Bernardik226/espnokia-phone/docs/assets/dash-status.png

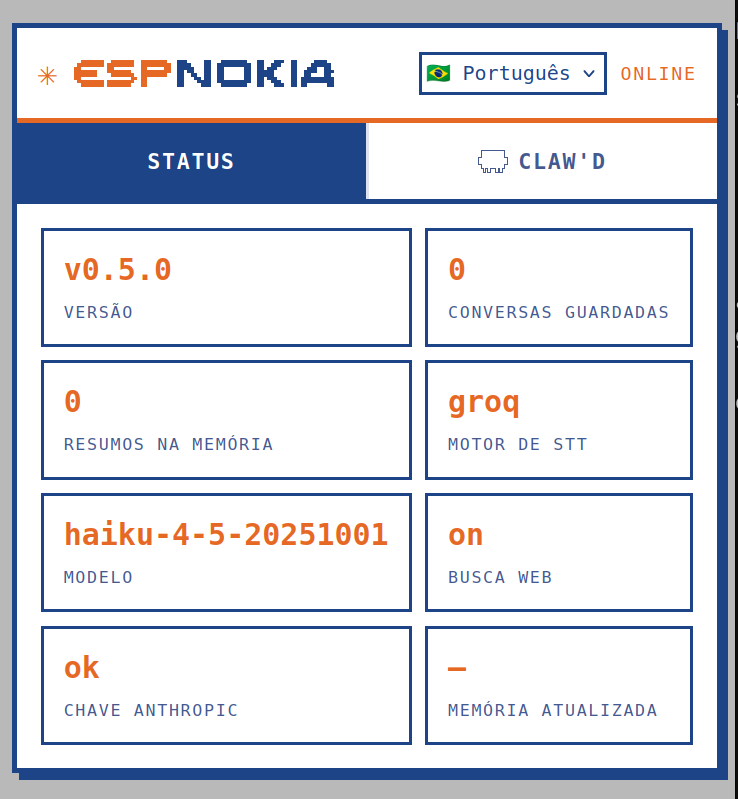
docs/assets/dash-status.png
