Bernardik226/espnokia-phone/docs/assets/photo-copa-menu.jpg

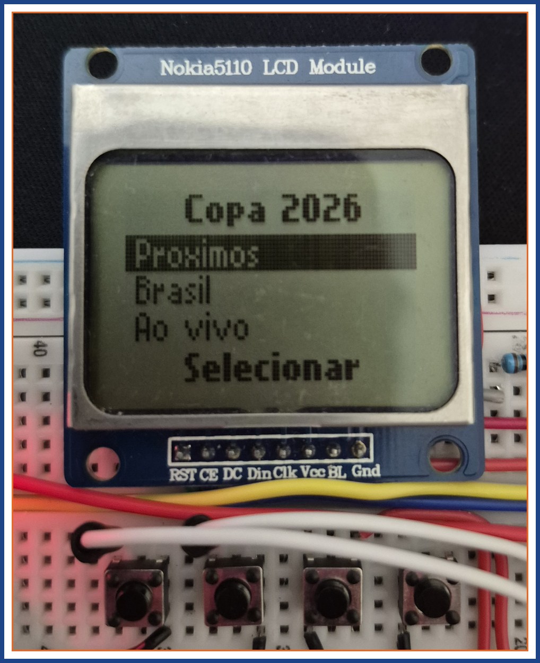
docs/assets/photo-copa-menu.jpg
