Bernardik226/espnokia-phone/docs/assets/photo-standby.jpg

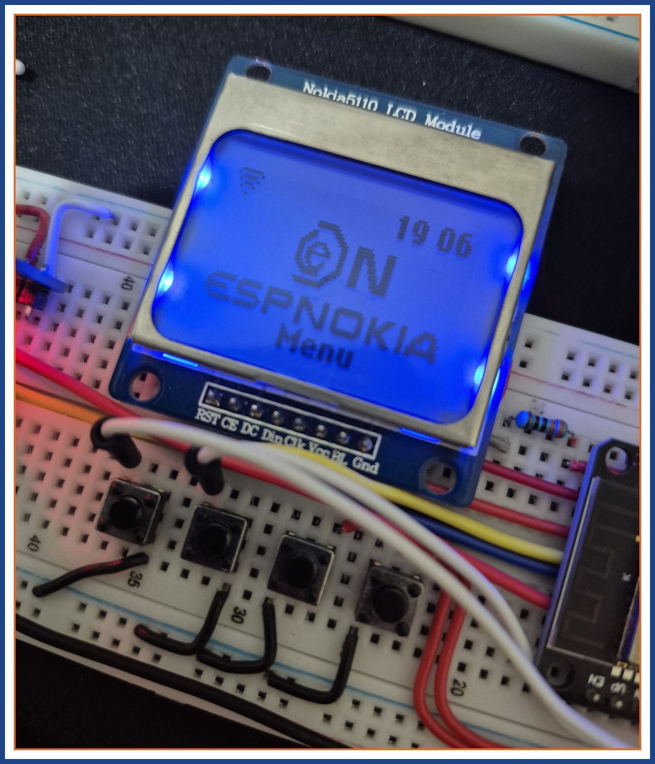
docs/assets/photo-standby.jpg
