Bernardik226/espnokia-phone/docs/assets/photos/clawd-listen.png

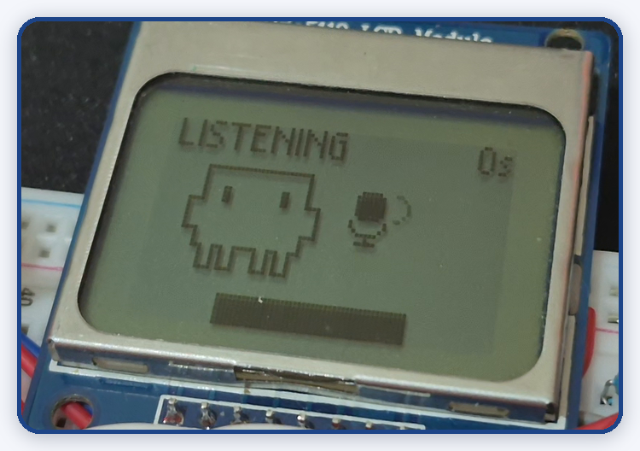
docs/assets/photos/clawd-listen.png
