Bernardik226/espnokia-phone/docs/assets/photos/clawd-reply.png

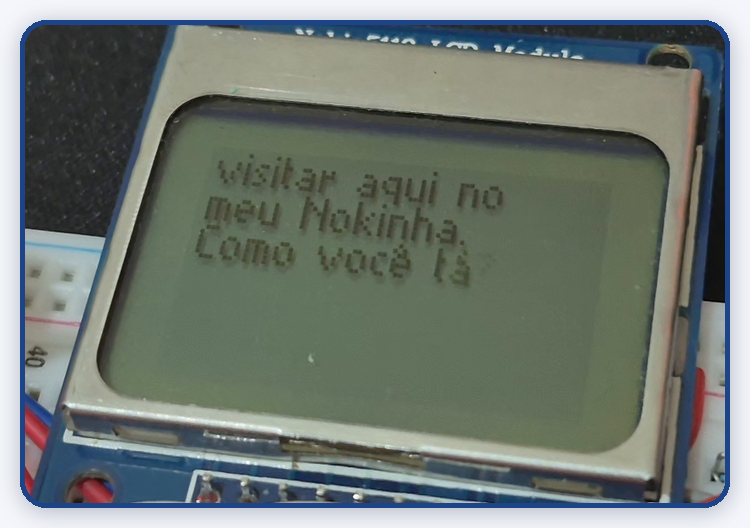
docs/assets/photos/clawd-reply.png
