Bernardik226/espnokia-phone/docs/assets/photos/clock.png

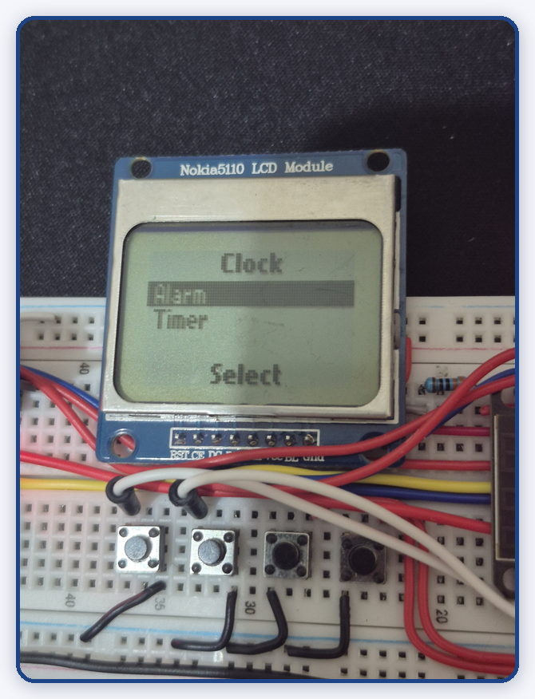
docs/assets/photos/clock.png
