Bernardik226/espnokia-phone/docs/assets/photos/connections.png

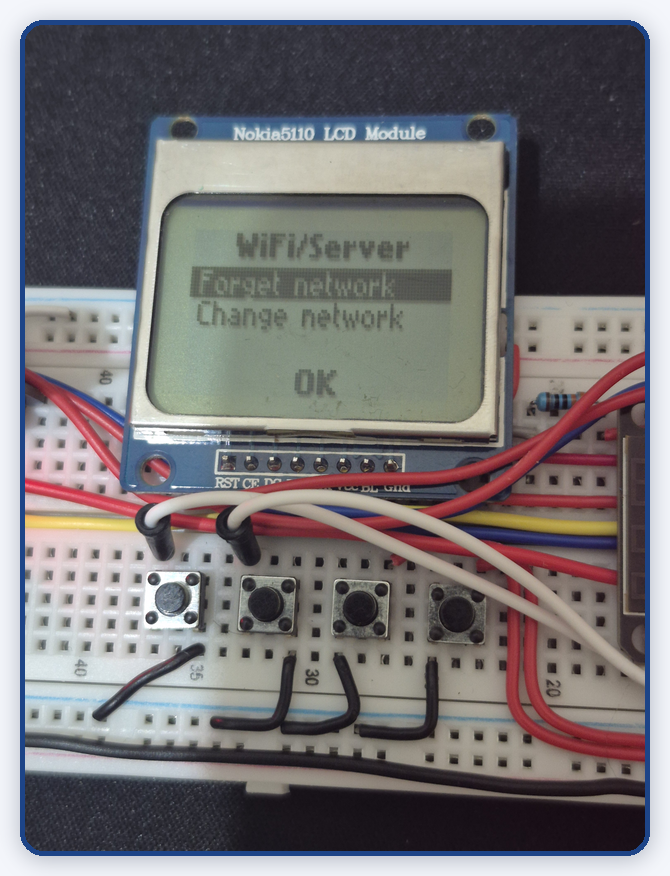
docs/assets/photos/connections.png
