Bernardik226/espnokia-phone/docs/assets/photos/copa-detail.png

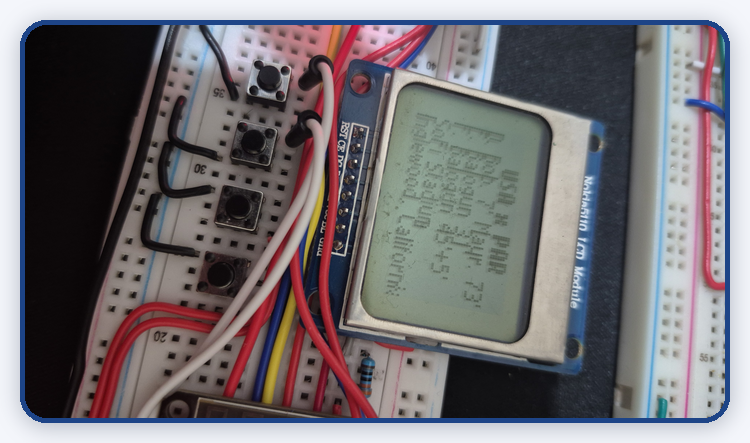
docs/assets/photos/copa-detail.png
