Bernardik226/espnokia-phone/docs/assets/photos/copa-list.png

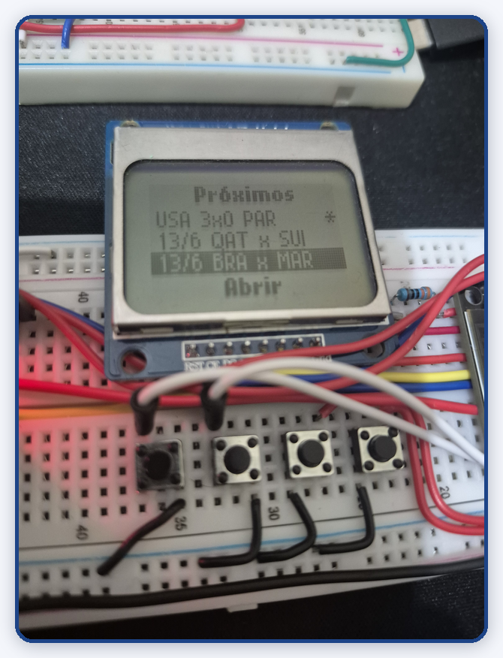
docs/assets/photos/copa-list.png
