Bernardik226/espnokia-phone/docs/assets/photos/copa-menu.png

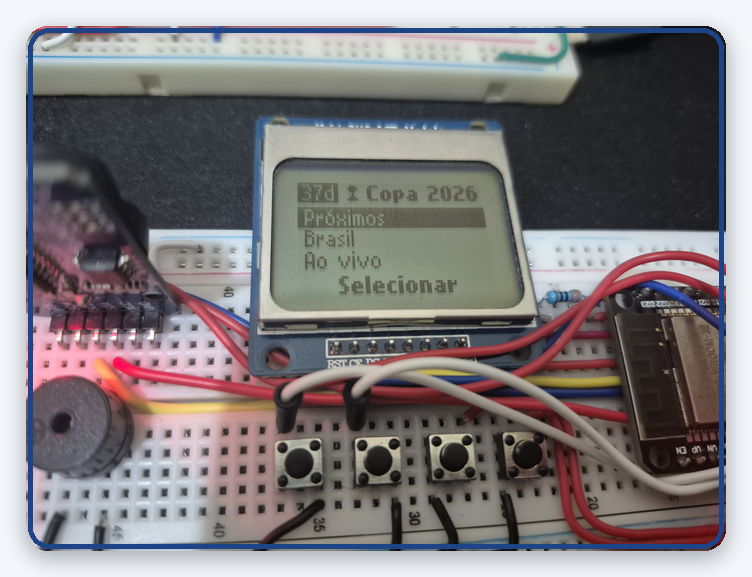
docs/assets/photos/copa-menu.png
