Bernardik226/espnokia-phone/docs/assets/photos/copa-notify.png

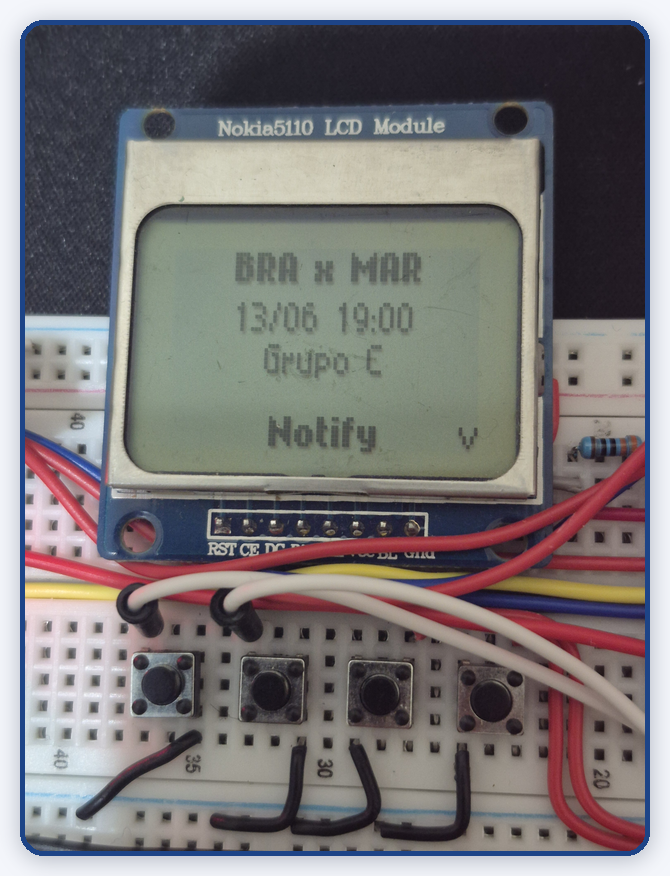
docs/assets/photos/copa-notify.png
