Bernardik226/espnokia-phone/docs/assets/photos/copa-upcoming.png

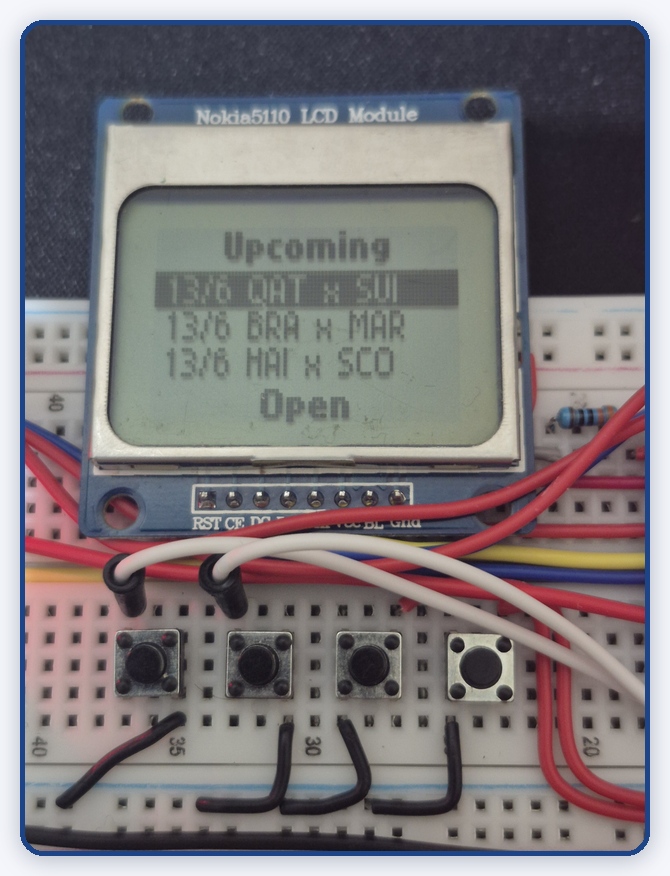
docs/assets/photos/copa-upcoming.png
