Bernardik226/espnokia-phone/docs/assets/photos/copa-worldcup.png

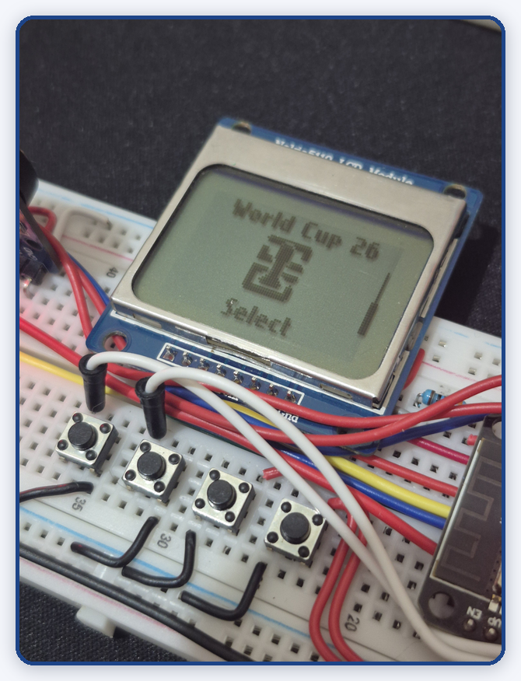
docs/assets/photos/copa-worldcup.png
