Bernardik226/espnokia-phone/docs/assets/photos/football-leagues.png

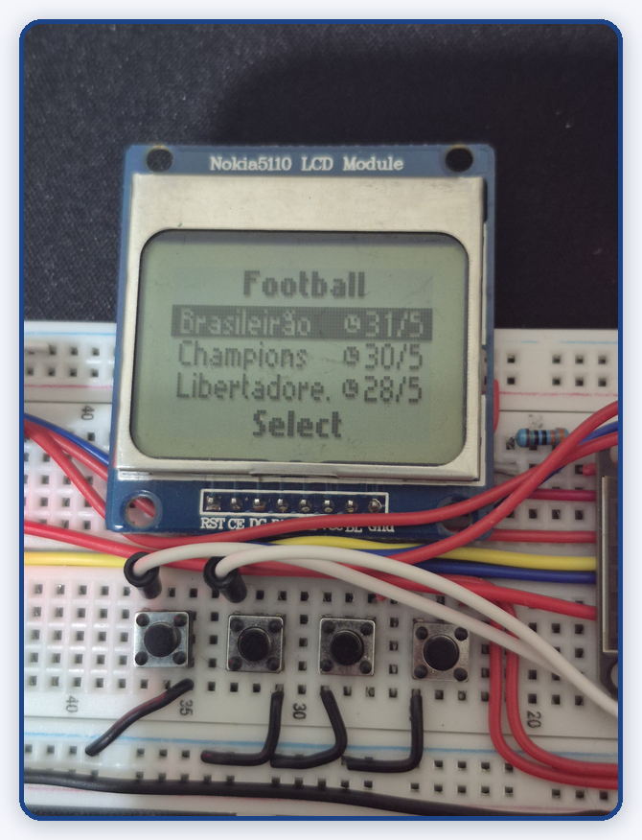
docs/assets/photos/football-leagues.png
