Bernardik226/espnokia-phone/docs/assets/photos/football-submenu.png

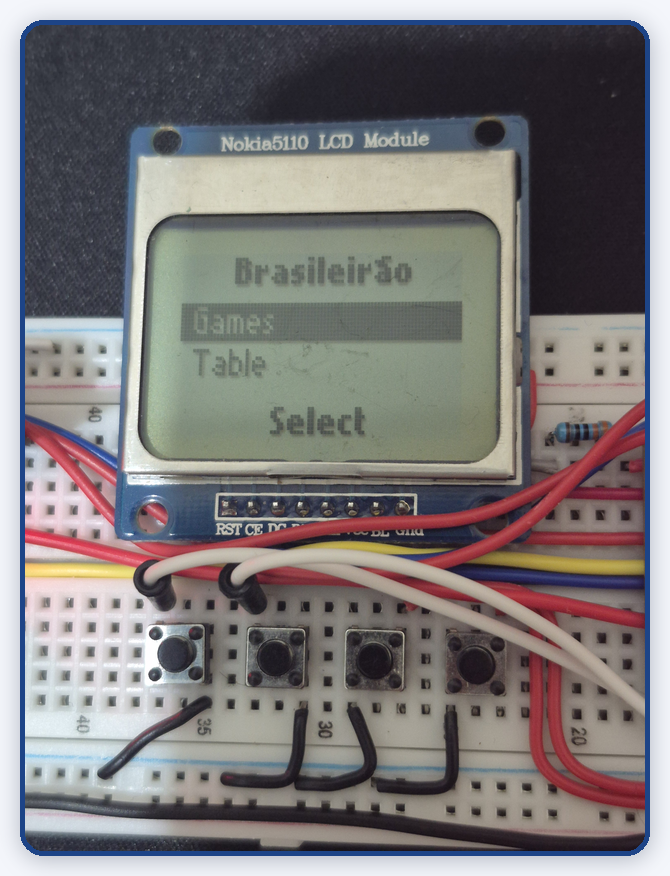
docs/assets/photos/football-submenu.png
