Bernardik226/espnokia-phone/docs/assets/photos/sports.png

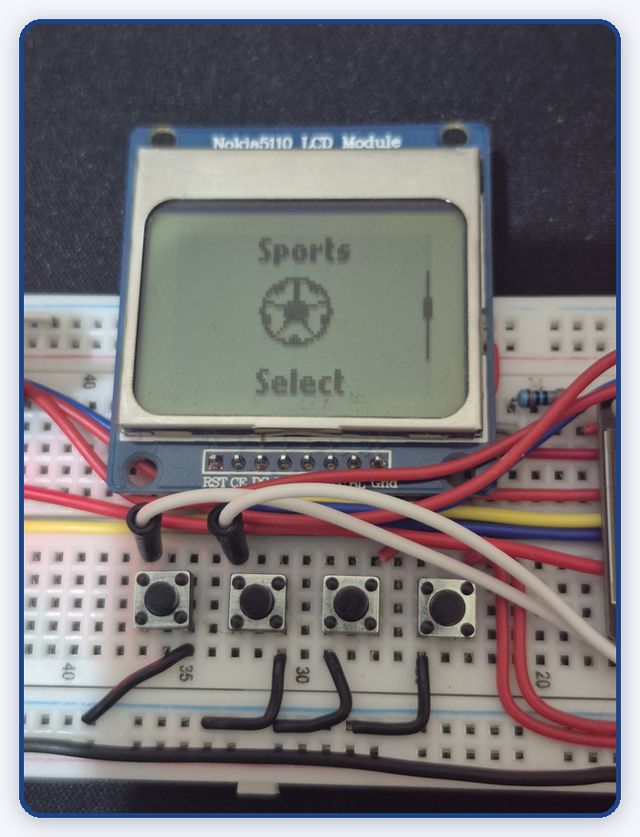
docs/assets/photos/sports.png
