Bernardik226/espnokia-phone/docs/assets/photos/standby.png

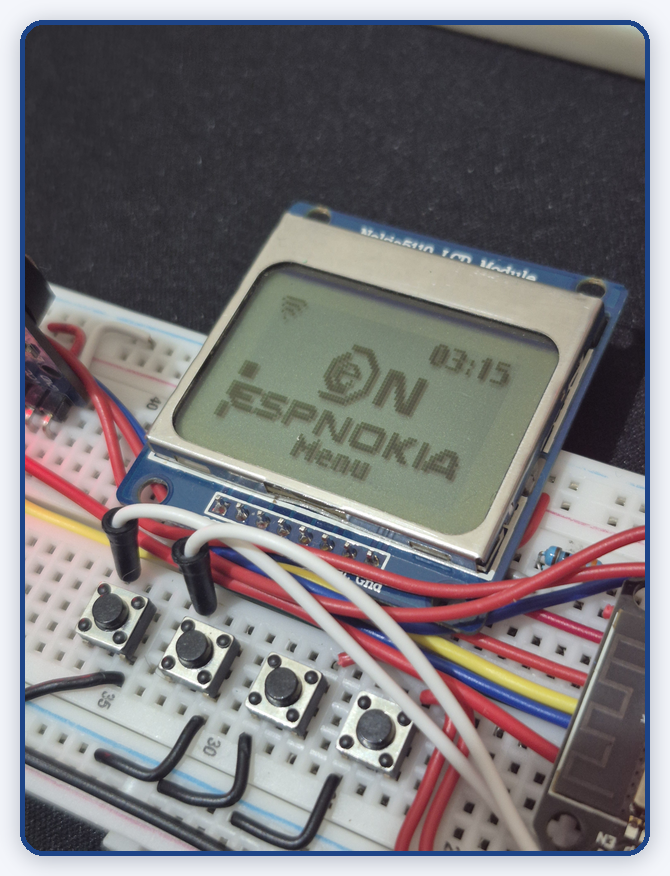
docs/assets/photos/standby.png
