Bernardik226/espnokia-phone/docs/assets/photos/weather.png

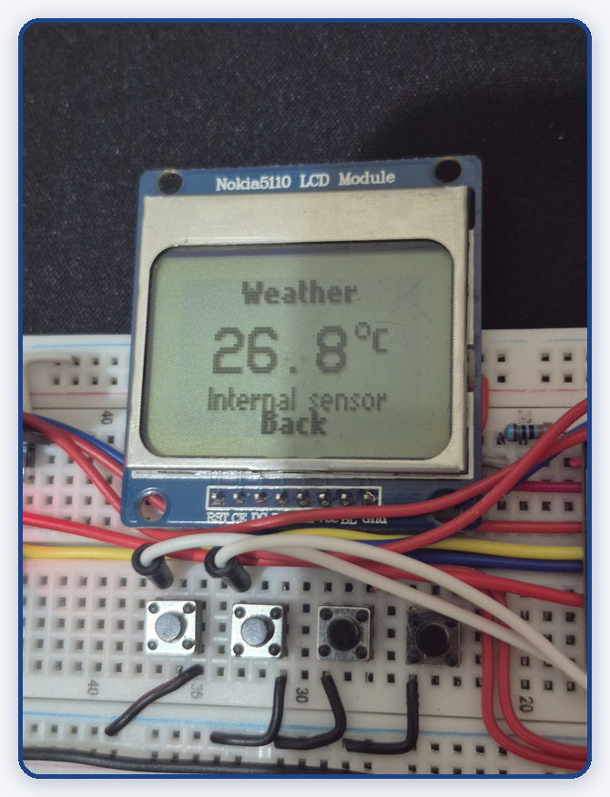
docs/assets/photos/weather.png
