Bernardik226/espnokia-phone/firmware/src/net/http.cpp

#include "net/http.h"
#include <Arduino.h>
#include <HTTPClient.h>
#include <WiFiClientSecure.h>
#include "net/conn.h"
#include "net/tls_client.h"
#include "net/wifi.h"

namespace http {

int get_json(const char* path, char* buf, size_t len) {
  if (!wifi::connected()) return -1;
  HTTPClient cli;
  cli.setTimeout(5000);
  String url = String(conn::server_url()) + path;
  WiFiClient plain;
  WiFiClientSecure tls;
  WiFiClient& conexao =
      *net::abrir_cliente(url.startsWith("https://"), plain, tls);
  if (!cli.begin(conexao, url)) return -2;
  cli.addHeader(conn::kHeaderDeviceKey, conn::device_key());
  int code = cli.GET();
  if (code == HTTP_CODE_OK) {
    String body = cli.getString();
    snprintf(buf, len, "%s", body.c_str());
  }
  cli.end();
  return code;
}

}  // namespace http
