Bernardik226/espnokia-phone/firmware/src/ui/assets.h

#pragma once
// GERADO por tools/grid2xbm.py — edite os grids em firmware/assets/ e regenere.
#include <U8g2lib.h>

#define NOKIA_LOGO_W 72
#define NOKIA_LOGO_H 8
static const unsigned char nokia_logo_bits[] U8X8_PROGMEM = {
    0x7f, 0x38, 0xfe, 0x1f, 0x07, 0x3e, 0x07, 0xf0, 0x01, 0xf7, 0x38, 0x0f,
    0x3c, 0x87, 0x0f, 0x07, 0xf8, 0x03, 0xf7, 0x38, 0x07, 0x38, 0xe7, 0x03,
    0x07, 0xfc, 0x07, 0xe7, 0x39, 0x07, 0x38, 0xff, 0x00, 0x07, 0x1e, 0x0f,
    0xe7, 0x39, 0x07, 0x38, 0xff, 0x00, 0x07, 0x0f, 0x1e, 0xc7, 0x3b, 0x07,
    0x38, 0xe7, 0x03, 0x87, 0xff, 0x3f, 0xc7, 0x3b, 0x0f, 0x3c, 0x87, 0x0f,
    0xc7, 0x03, 0x78, 0x87, 0x3f, 0xfe, 0x1f, 0x07, 0x3e, 0xe7, 0x01, 0xf0,
};

#define HAND_LEFT_W 49
#define HAND_LEFT_H 31
static const unsigned char hand_left_bits[] U8X8_PROGMEM = {
    0x00, 0x01, 0x10, 0x00, 0x00, 0x00, 0x00, 0x20, 0x80, 0x80, 0x00, 0x00,
    0x00, 0x00, 0x00, 0x20, 0x20, 0x20, 0x01, 0x00, 0x00, 0x80, 0x48, 0x49,
    0x80, 0x00, 0x00, 0x00, 0x00, 0xa4, 0xb6, 0x21, 0x01, 0x00, 0x00, 0x20,
    0xd5, 0xff, 0xd7, 0x01, 0x00, 0x00, 0x88, 0xe8, 0x56, 0x7d, 0x00, 0x00,
    0x00, 0x60, 0xb7, 0x03, 0x00, 0x00, 0x00, 0x00, 0x5a, 0xff, 0x05, 0x00,
    0x00, 0x00, 0x00, 0xb0, 0x6f, 0x0f, 0x00, 0x00, 0x00, 0x00, 0xd0, 0xff,
    0x37, 0x00, 0x00, 0x00, 0x00, 0x78, 0xdf, 0x5a, 0x00, 0x00, 0x00, 0x00,
    0xd0, 0x7f, 0x67, 0x00, 0x00, 0x00, 0x00, 0xa0, 0xd6, 0x9a, 0x00, 0x00,
    0x00, 0x00, 0x50, 0xaf, 0x21, 0x2d, 0x40, 0x18, 0x00, 0xa0, 0x56, 0x08,
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
    0x00, 0x00, 0x00, 0x00, 0x7e, 0x07, 0x00, 0x00, 0x00, 0x00, 0x00, 0x00,
    0x00, 0x00, 0x00, 0x00, 0x00, 0x00, 0x00, 0x00, 0x00, 0x00, 0x00, 0x00,
    0x00, 0x00, 0x00, 0x00, 0x00, 0x00, 0x00, 0x00, 0x00, 0x00, 0x00, 0x00,
    0x00, 0x00, 0x00, 0x00, 0x00, 0x00, 0x00, 0x00,
};
