Bernardik226/espnokia-phone/firmware/src/ui/nokia_ui.cpp

#include "nokia_ui.h"
#include <stdio.h>
#include <string.h>
#include "assets.h"
#include "fonts3310.h"
#include "i18n.h"

namespace nokia_ui {

// estrelinha 5x5 (sparkle de 4 pontas) — miolo cheio pra ler bem no 1-bit
void draw_star(U8G2& g, int x, int y) {
  g.drawVLine(x + 2, y, 5);
  g.drawHLine(x, y + 2, 5);
  g.drawPixel(x + 1, y + 1); g.drawPixel(x + 3, y + 1);
  g.drawPixel(x + 1, y + 3); g.drawPixel(x + 3, y + 3);
}
int hiscore_w(U8G2& g, uint32_t value) {
  char b[16]; snprintf(b, sizeof(b), "HS%lu", (unsigned long)value);
  const uint8_t* prev = g.getU8g2()->font;
  g.setFont(u8g2_font_4x6_tr);
  int w = 6 + (int)g.getStrWidth(b);   // 5px estrela + 1 de folga + texto
  if (prev) g.setFont(prev);
  return w;
}
void hiscore(U8G2& g, int x, int y, uint32_t value) {
  const uint8_t* prev = g.getU8g2()->font;
  draw_star(g, x, y + 1);
  char b[16]; snprintf(b, sizeof(b), "HS%lu", (unsigned long)value);
  g.setFont(u8g2_font_4x6_tr);
  g.drawStr(x + 6, y + 6, b);
  if (prev) g.setFont(prev);
}
// negrito real (fonte 3310 small bold), preservando a fonte corrente do
// caller; drawUTF8 em vez de drawStr pra aceitar os acentos das traducoes
void text_bold(U8G2& g, int x, int y, const char* s) {
  const uint8_t* prev = g.getU8g2()->font;
  g.setFont(u8g2_font_3310_small_bold);
  g.drawUTF8(x, y, s);
  if (prev) g.setFont(prev);
}
void text_bold_center(U8G2& g, int y, const char* s) {
  const uint8_t* prev = g.getU8g2()->font;
  g.setFont(u8g2_font_3310_small_bold);
  g.drawUTF8(42 - (int)g.getUTF8Width(s) / 2, y, s);
  if (prev) g.setFont(prev);
}
void text_center(U8G2& g, int y, const char* s) {
  g.drawUTF8(42 - (int)g.getUTF8Width(s) / 2, y, s);
}
int bold_width(U8G2& g, const char* s) {
  const uint8_t* prev = g.getU8g2()->font;
  g.setFont(u8g2_font_3310_small_bold);
  int w = (int)g.getUTF8Width(s);
  if (prev) g.setFont(prev);
  return w;
}
void softkey(U8G2& g, const char* label) { text_bold_center(g, 47, label); }

void softkey_action(U8G2& g, const char* label, bool up_held) {
  softkey(g, label);
  int cx = 80, cy = 44, r = 2;                 // canto inferior direito
  if (up_held) g.drawDisc(cx, cy, r);          // acesa no hold
  else g.drawCircle(cx, cy, r);                // solta: só o contorno
}
void list_row(U8G2& g, int y, uint8_t w, const char* text, bool selected) {
  if (selected) { g.drawBox(0, y, w, 9); g.setDrawColor(0); }
  g.drawUTF8(3, y + 8, text);
  if (selected) g.setDrawColor(1);
}
void inv_str(U8G2& g, int x, int baseline, const char* s) {
  g.drawBox(x - 1, baseline - 7, (int)g.getStrWidth(s) + 2, 9);
  g.setDrawColor(0);
  g.drawStr(x, baseline, s);
  g.setDrawColor(1);
}
void poda(U8G2& g, char* s, int max_w) {
  if ((int)g.getUTF8Width(s) <= max_w) return;
  size_t n = strlen(s);
  while (n > 1) {
    do { n--; } while (n > 1 && (s[n] & 0xC0) == 0x80);  // char UTF-8 inteiro
    s[n] = '.';
    s[n + 1] = '\0';
    if ((int)g.getUTF8Width(s) <= max_w) return;
  }
}
void no_network(U8G2& g) {
  g.drawXBMP((84 - ICON_NOWIFI_W) / 2, 11, ICON_NOWIFI_W, ICON_NOWIFI_H,
             icon_nowifi_bits);
  text_center(g, 38, tr(STR_CONNECT_WIFI));
}
}  // namespace nokia_ui
