Bernardik226/espnokia-phone/firmware/src/ui/nokia_ui.h

#pragma once
#include <U8g2lib.h>

// Idioma visual do 3310: negrito real (fonte 3310 small bold, fonts3310.h)
// e softkey label centralizado na base da tela.
namespace nokia_ui {
// negrito 3310; (x, y) = baseline, como drawStr; preserva a fonte corrente
void text_bold(U8G2& g, int x, int y, const char* s);
// campo selecionado do editor: caixa preenchida + texto em cor invertida
// (x, baseline) = onde drawStr(s) desenharia; a caixa cerca esse retangulo
void inv_str(U8G2& g, int x, int baseline, const char* s);
// negrito centrado horizontalmente (tela de 84px); y = baseline
void text_bold_center(U8G2& g, int y, const char* s);
// centralizado horizontalmente na fonte corrente (sem forcar negrito);
// y = baseline, como drawStr
void text_center(U8G2& g, int y, const char* s);
// largura do texto na fonte negrito (pra alinhar sem desenhar)
int bold_width(U8G2& g, const char* s);
// label de softkey centrado na base (negrito 3310, baseline 47)
void softkey(U8G2& g, const char* label);
// como softkey, mas com a bolinha do BOTÃO DE AÇÃO (UP) no canto inf-direito:
// contorno quando solto, preenchida (acesa) enquanto up_held — dica visual da
// tecla de ação/alternância que o app oferece naquela tela
void softkey_action(U8G2& g, const char* label, bool up_held);
// estrelinha 5x5 (canto sup-esq em x,y) — usada no badge de recorde
void draw_star(U8G2& g, int x, int y);
// badge de recorde PADRÃO dos jogos: estrela + "HS" + valor (fonte 4x6), com
// o topo em (x,y). hiscore_w devolve a largura pra alinhar à direita.
void hiscore(U8G2& g, int x, int y, uint32_t value);
int hiscore_w(U8G2& g, uint32_t value);
// uma linha de lista na posicao y; se selected, barra invertida de
// largura w (box em (0,y,w,9), texto em x=3,y+8) — nao cuida de
// windowing/scrollbar, so a linha; o caller decide o que mais desenhar
// na mesma linha (marcadores etc) e, se precisar, reusa o color(0) do
// caller enquanto selected pra manter o efeito invertido
void list_row(U8G2& g, int y, uint8_t w, const char* text, bool selected);
// tela padrao dos apps com internet sem rede: wifi cortado + instrucao
// (titulo e softkey ficam por conta do app)
void no_network(U8G2& g);
// poda s in place ate caber em max_w, marcando o corte com '.' — sem partir
// caractere UTF-8 no meio (estilo 3310: "Premier League" → "Premier Lea.")
void poda(U8G2& g, char* s, int max_w);
}  // namespace nokia_ui
