Bernardik226/espnokia-phone/firmware/include/espnokia_config.example.h

#pragma once
// copie para espnokia_config.h (gitignored) e preencha.
// o WiFi nao fica aqui: configure pela pagina web do modo AP (Config > Wifi)
#define SERVER_URL  "http://192.168.0.10:8000"  // sem barra no fim
#define DEVICE_KEY  "troque-esta-chave"
